beustens/DetectorReader/hardware/Simulation/demod_single_transistor.asc

B1: bv; V=V(Pulse)+0.005*white(10e6*time)
B2: bv; V=V(PulseReader)+V(PulseTag)
C1: cap; 1n
C2: cap; 100n
C3: cap; 100p
C4: cap; 1n
Q1: npn; BC847C
Q2: npn; BC847C
R1: res; 1k
R2: res; 10k
R3: res; 1Meg
R4: res; 10k
R5: res; 10k
R6: res; 220k
R7: res; 220k
R8: res; 100
R9: res; 1k
U1: RH111
V1: voltage; 3
V3: voltage; PULSE(5 0 {Pad-150n} 100n 100n {NReader*PReader-PReader/2+100n})
V4: voltage; PULSE(1 5m {Pad} 10n 10n {PReader/2} {PReader} {NReader})
V5: voltage; PULSE(0 5m {Pad+NReader*PReader-PReader/2+Sep} 10n 10n {(1/FTag)/2} {1/FTag} {NTag})
Named nets: 0, Supply, CmdInv, Signal, PulseReader, PulseTag, Pulse, Avr, Amp, Comp
.tran {Pad+NReader*PReader+Sep+NTag/FTag+Pad}
.param Pad=100u Sep=30u PReader=20u FTag=50k NReader=5 NTag=10
