beustens/DetectorReader/hardware/Simulation/freq-response_dual-stage.asc

C1: cap; 10n
C2: cap; 1n
C3: cap; 10n
C4: cap; 1n
C5: cap; 1n
C9: cap; 1µ
C10: cap; 1µ
C11: cap; 27p
C12: cap; 10n
C13: cap; 47p
Q1: npn; BC847C
Q2: npn; BC847C
R1: res; 1k
R2: res; 220k
R3: res; 1k
R4: res; 220k
R5: res; 1k
R13: res; 1k
R14: res; 33k
R15: res; 1k
R16: res; 33k
R17: res; 10k
R18: res; 10k
U2: opamp2; TL972
U3: opamp2; TL972
V1: voltage; ""; AC 1
V2: voltage; 3
Named nets: 0, Supply, Signal, CM, Amp2, Amp1
.ac dec 1000 10 10Meg
.include models/TL972.lib
