beustens/DetectorReader/hardware/Simulation/demod_dual_op-amp.asc

B1: bv; V=V(Pulse)+0.005*white(10e6*time)
B2: bv; V=V(PulseReader)+V(PulseTag)
C1: cap; 10p
C2: cap; 4.7n
C3: cap; 1p
C4: cap; 1µ
Q1: npn; BC547B
R1: res; 1k
R2: res; 10k
R3: res; 100
R5: res; 10k
R7: res; 10k
R8: res; 5.1k
R9: res; 220k
R10: res; 10k
R14: res; 220k
U3: opamp2; TL972
U4: opamp2; TL972
V1: voltage; 5
V3: voltage; PULSE(5 0 {Pad-150n} 100n 100n {NReader*PReader-PReader/2+100n})
V4: voltage; PULSE(1 5m {Pad} 10n 10n {PReader/2} {PReader} {NReader})
V5: voltage; PULSE(0 5m {Pad+NReader*PReader-PReader/2+Sep} 10n 10n {(1/FTag)/2} {1/FTag} {NTag})
Named nets: 0, Supply, CmdInv, Amp1, Signal, PulseReader, PulseTag, Pulse, CM, Comp, Switched
.tran {Pad+NReader*PReader+Sep+NTag/FTag+Pad}
.param Pad=100u Sep=30u PReader=20u FTag=50k NReader=5 NTag=10
.include models/TL972.lib
