beustens/DetectorReader/hardware/Simulation/demod_quad_opv.asc

B1: bv; V=V(Pulse)+0.005*white(10e6*time)
B2: bv; V=V(PulseReader)+V(PulseTag)
C1: cap; 120p
C2: cap; 4.7n
C6: cap; 120p
C7: cap; 4.7n
D1: diode; 1N4148
D2: diode; 1N4148
Q1: npn; BC547B
R1: res; 1k
R4: res; 1k
R5: res; 1k
R6: res; 27k
R8: res; 10k
R9: res; 27k
R14: res; 100k
U2: opamp2; ba4584r_sub
U3: opamp2; ba4584r_sub
U4: opamp2; ba4584r_sub
V1: voltage; 5
V2: voltage; 3
V3: voltage; PULSE(5 0 {Pad-150n} 100n 100n {NReader*PReader-PReader/2+100n})
V4: voltage; PULSE(1 5m {Pad} 10n 10n {PReader/2} {PReader} {NReader})
V5: voltage; PULSE(0 5m {Pad+NReader*PReader-PReader/2+Sep} 10n 10n {(1/FTag)/2} {1/FTag} {NTag})
Named nets: 0, Supply, CmdInv, Amp1, Signal, PulseReader, PulseTag, Pulse, CM, Amp2, Comp
.tran {Pad+NReader*PReader+Sep+NTag/FTag+Pad}
.param Pad=100u Sep=30u PReader=20u FTag=50k NReader=5 NTag=10
.include models/BA4584R_Rev002.lib
